EmersonAlbertini/PROJETO-DE-BANCO-DE-CAPACITORES-PARA-CORRECAO-DO-FATOR-DE-POTENCIA-EM-UMA-INDUSTRIA-ALIMENTICIA-/Cálculo_de_Climatização/PROJETO DE BANCO DE CAPACITORES - 225kVAr_20250828_020039_documentation.pdf

# RiTherm

# Summary

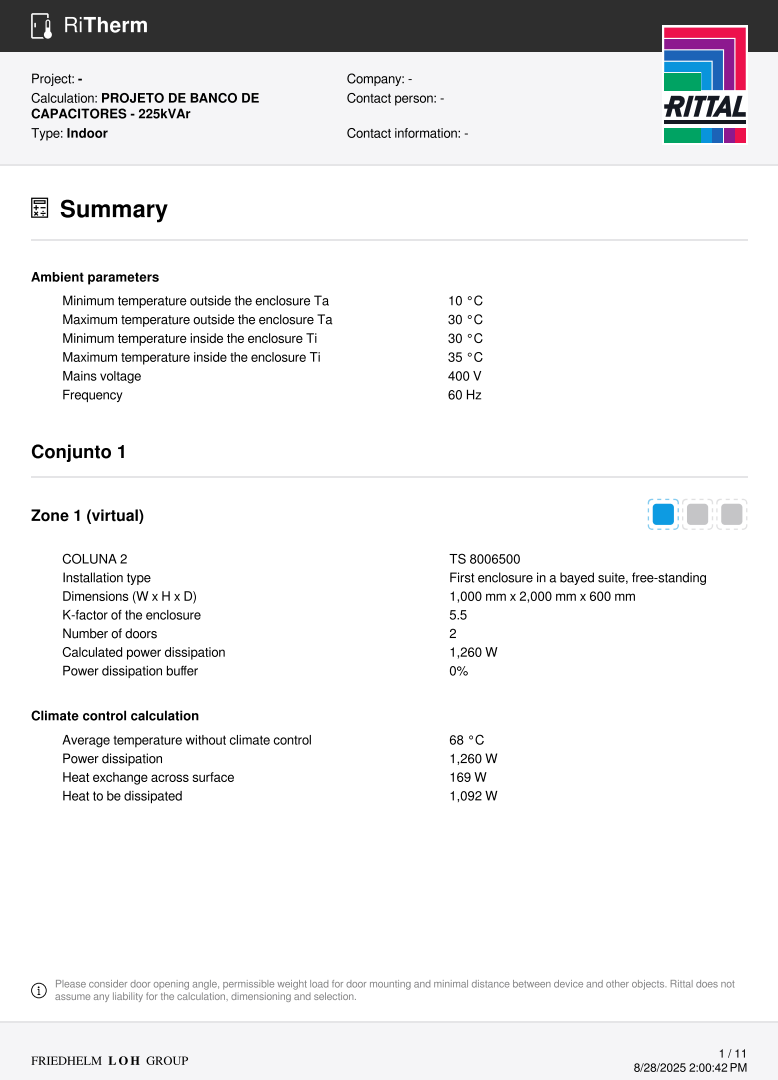
[picture p50: page 1]
Company: -; Contact person: -; Contact information: -; Ambient parameters; Minimum temperature outside the enclosure Ta; Maximum temperature outside the enclosure Ta; Minimum temperature inside the enclosure Ti; Maximum temperature inside the enclosure Ti; Mains voltage; Frequency; Conjunto 1; Zone 1 (virtual); COLUNA 2; Installation type; First enclosure in a bayed suite, free-standing; Dimensions (W x H x D); K-factor of the enclosure; Number of doors; Calculated power dissipation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

Project: -
Calculation: PROJETO DE BANCO DE
CAPACITORES - 225kVAr
Type: Indoor

Climate control calculation

Please consider door opening angle, permissible weight load for door mounting and minimal distance between device and other objects. Rittal does not
assume any liability for the calculation, dimensioning and selection.

## Order overview

Measures to maintain the temperature

The chosen climate control solution for this virtual zone has a different IP rating than the ones in neighbouring zones.

Part number | SK3244740 + SK3243300 chopped-fibre filter
Device type | Fan-and-filter unit
Cooling output | 1,174 m³/h
Necessary air throughput | 765 m³/h
Device mounting | Wall-mounted
IP rating | 54
Quantity | 2

### Zone 2 (virtual)

COLUNA 3 | TS 8606500
Installation type | Enclosure within a bayed suite, free-standing
Dimensions (W x H x D) | 600 mm x 2,000 mm x 600 mm
K-factor of the enclosure | 5.5
Number of doors | 1
Calculated power dissipation | 650 W
Power dissipation buffer | 0%

Climate control calculation

Average temperature without climate control | 61 °C
Power dissipation | 650 W
Heat exchange across surface | 107 W
Heat to be dissipated | 544 W

Please consider door opening angle, permissible weight load for door mounting and minimal distance between device and other objects. Rittal does not assume any liability for the calculation, dimensioning and selection.

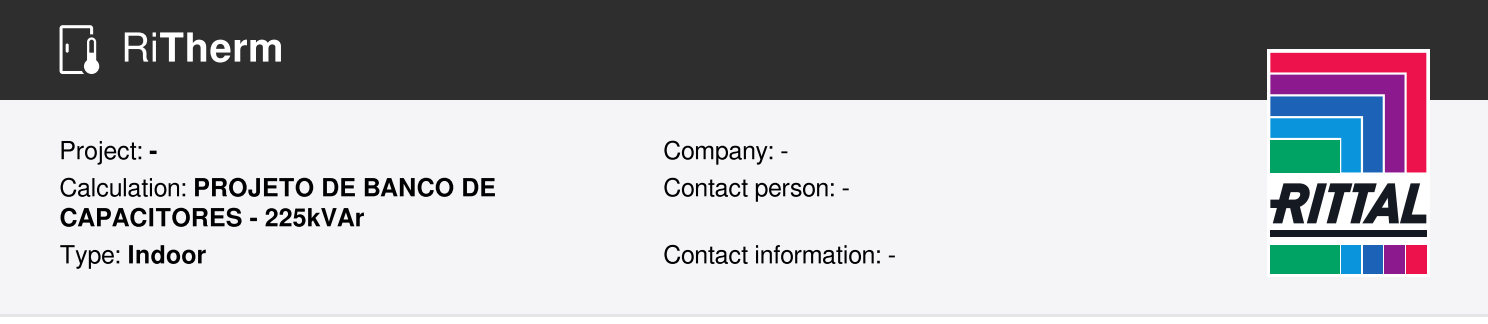
[picture p51: figure]
Calculation: PROJETO DE BANCO DE CAPACITORES - 225kVAr Type: Indoor; Contact person: -; Contact information: -

## Order overview

Measures to maintain the temperature

The chosen climate control solution for this virtual zone has a different IP rating than the ones in neighbouring zones.

Part number | SK3140140 + SK3243200 chopped-fibre filter
Device type | Fan-and-filter unit
Cooling output | 565 m³/h
Air throughput, unimpeded air flow | 853 m³/h
Necessary air throughput | 381 m³/h
Device mounting | Roof-mounted
IP rating | 55
Quantity | 1

### Zone 3 (virtual)

COLUNA 4 | TS 8606500
Installation type | Last enclosure in a bayed suite, free-standing
Dimensions (W x H x D) | 600 mm x 2,000 mm x 600 mm
K-factor of the enclosure | 5.5
Number of doors | 1
Calculated power dissipation | 650 W
Power dissipation buffer | 0%

Climate control calculation

Average temperature without climate control | 58 °C
Power dissipation | 650 W
Heat exchange across surface | 120 W
Heat to be dissipated | 531 W

Please consider door opening angle, permissible weight load for door mounting and minimal distance between device and other objects. Rittal does not assume any liability for the calculation, dimensioning and selection.

## Order overview

Measures to maintain the temperature

The chosen climate control solution for this virtual zone has a different IP rating than the ones in neighbouring zones.

Part number | SK3140140 + SK3243200 chopped-fibre filter
Device type | Fan-and-filter unit
Cooling output | 565 m³/h
Air throughput, unimpeded air flow | 853 m³/h
Necessary air throughput | 372 m³/h
Device mounting | Roof-mounted
IP rating | 55
Quantity | 1

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

# Component list

## Enclosure set: Conjunto 1 (Zone 1)

## COLUNA 2 - TS 8006500

No component list was created for this enclosure. The calculation was performed using the entered power dissipation and simultaneity factor.

Entered power
dissipation

Entered simultaneity
factor
| | Power dissipation buffer | Calculated power dissipation
1,260 W | 100% | 0% | 1,260 W

## Enclosure set: Conjunto 1 (Zone 2)

## COLUNA 3 - TS 8606500

No component list was created for this enclosure. The calculation was performed using the entered power dissipation and simultaneity factor.

Entered power dissipation | Entered simultaneity factor | Power dissipation buffer | Calculated power dissipation
650 W | 100% | 0% | 650 W

## Enclosure set: Conjunto 1 (Zone 3)

## COLUNA 4 - TS 8606500

No component list was created for this enclosure. The calculation was performed using the entered power dissipation and simultaneity factor.

Entered power dissipation | Entered simultaneity factor | Power dissipation buffer | Calculated power dissipation
650 W | 100% | 0% | 650 W

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

Verification of temperature rise according to IEC 60890, as required in DIN EN 61439

Customer / order: PROJETO DE BANCO DE CAPACITORES - 225kVAr - Conjunto 1 - Zone 1 Enclosure type: Single enclosure COLUNA 2 (8006500)

Decisive dimensions for temperature
rise

Height: 2,000 mm
Width: 1,000 mm
Depth: 600 mm

Installation type: Single enclosure, free-standing

Decisive dimensions for temperature rise | | Dimensions | A0 | Area factor b acc. to table 3 | Ae (Sp. 3) x (Sp. 4)
| | m x m | m² | | m²
| | 2 | 3 | 4 | 5
| Roof | 1.00 x 0.60 | 0.60 | 0.90 | 0.54
| Floor | 1.00 x 0.60 | 0.60 | 0.50 | 0.30
| Front | 1.00 x 2.00 | 2.00 | 0.90 | 1.80
| Rear | 1.00 x 2.00 | 2.00 | 0.90 | 1.80
| Left side | 0.60 x 2.00 | 1.20 | 0.90 | 1.08
| Right side | 0.60 x 2.00 | 1.20 | 0.50 | 0.60

Ae = ∑(AO - b) = 6.12

With effective cooling surface Ae
> 1.25 m² | ≤ 1.25 m²
ƒ = h¹.35 ÷ Ab = 4.25 (see 5.2.3) | g = h ÷ w = (see 5.2.3)
Air inlet openings [cm²] | 0
Enclosure constant k | 0.144
Factor for horizontal divider panels d | 1.00
Effective power dissipation W | 1,260.00
P x = P*** | 310.96
Δt0.5 = k × d × Px [K] | 44.68
Temperature distribution factor c | 1.39
Δt1.0 = c × Δt 0.5 [K] | 62.04

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

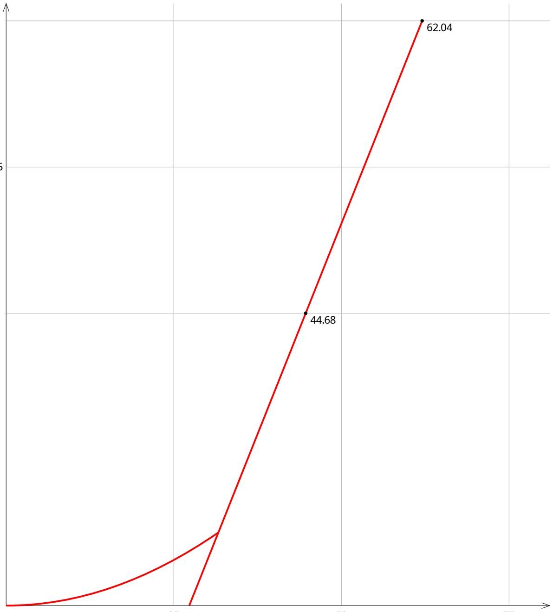
[picture p52: figure]

25 | 50 | 75

1.0

0.75

0.5

### Excess air temperature Δt inside the enclosure →

### Multiple of enclosure height →

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

Verification of temperature rise according to IEC 60890, as required in DIN EN 61439

Customer / order: PROJETO DE BANCO DE CAPACITORES - 225kVAr - Conjunto 1 - Zone 2 Enclosure type: Single enclosure COLUNA 3 (8606500)

Decisive dimensions for temperature
rise

Height: 2,000 mm
Width: 600 mm
Depth: 600 mm

Installation type: Single enclosure, free-standing

Decisive dimensions for temperature rise | | Dimensions | A0 | Area factor b acc. to table 3 | Ae (Sp. 3) x (Sp. 4)
| | m x m | m² | | m²
| | 2 | 3 | 4 | 5
| Roof | 0.60 x 0.60 | 0.36 | 0.90 | 0.32
| Floor | 0.60 x 0.60 | 0.36 | 0.50 | 0.18
| Front | 0.60 x 2.00 | 1.20 | 0.90 | 1.08
| Rear | 0.60 x 2.00 | 1.20 | 0.90 | 1.08
| Left side | 0.60 x 2.00 | 1.20 | 0.50 | 0.60
| Right side | 0.60 x 2.00 | 1.20 | 0.50 | 0.60

Ae = ∑(AO - b) = 3.86

With effective cooling surface Ae
> 1.25 m² | ≤ 1.25 m²
ƒ = h¹.35 ÷ Ab = 7.08 (see 5.2.3) | g = h ÷ w = (see 5.2.3)
Air inlet openings [cm²] | 0
Enclosure constant k | 0.205
Factor for horizontal divider panels d | 1.00
Effective power dissipation W | 650.00
P x = P*** | 182.63
Δt0.5 = k × d × Px [K] | 37.49
Temperature distribution factor c | 1.49
Δt1.0 = c × Δt 0.5 [K] | 55.78

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

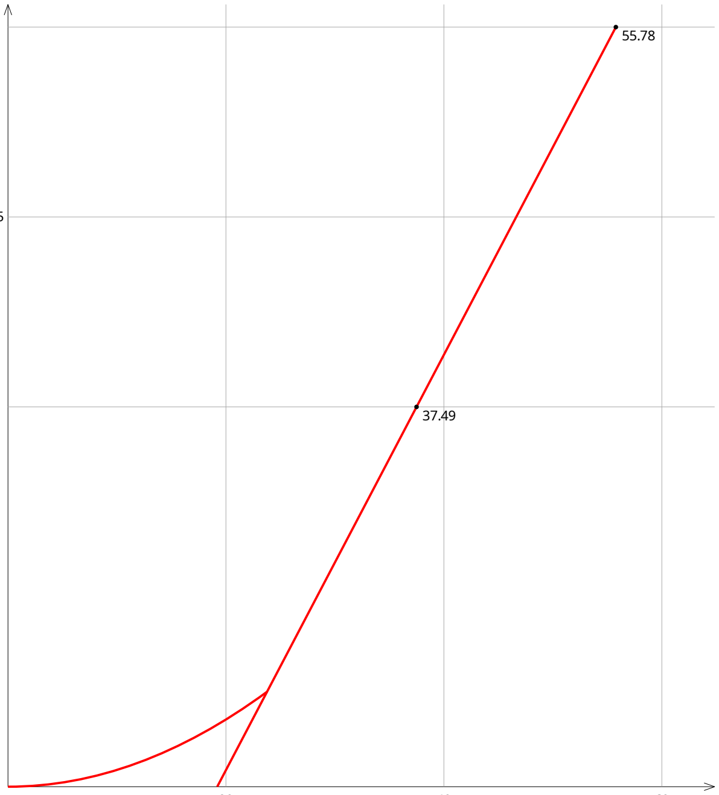
[picture p53: figure]

20 | 40 | 60

1.0

0.75

0.5

### Excess air temperature Δt inside the enclosure →

### Multiple of enclosure height →

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

Verification of temperature rise according to IEC 60890, as required in DIN EN 61439

Customer / order: PROJETO DE BANCO DE CAPACITORES - 225kVAr - Conjunto 1 - Zone 3 Enclosure type: Single enclosure COLUNA 4 (8606500)

Decisive dimensions for temperature
rise

Height: 2,000 mm
Width: 600 mm
Depth: 600 mm

Installation type: Single enclosure, free-standing

Decisive dimensions for temperature rise | | Dimensions | A0 | Area factor b acc. to table 3 | Ae (Sp. 3) x (Sp. 4)
| | m x m | m² | | m²
| | 2 | 3 | 4 | 5
| Roof | 0.60 x 0.60 | 0.36 | 0.90 | 0.32
| Floor | 0.60 x 0.60 | 0.36 | 0.50 | 0.18
| Front | 0.60 x 2.00 | 1.20 | 0.90 | 1.08
| Rear | 0.60 x 2.00 | 1.20 | 0.90 | 1.08
| Left side | 0.60 x 2.00 | 1.20 | 0.50 | 0.60
| Right side | 0.60 x 2.00 | 1.20 | 0.90 | 1.08

Ae = ∑(AO - b) = 4.34

With effective cooling surface Ae
> 1.25 m² | ≤ 1.25 m²
ƒ = h¹.35 ÷ Ab = 7.08 (see 5.2.3) | g = h ÷ w = (see 5.2.3)
Air inlet openings [cm²] | 0
Enclosure constant k | 0.187
Factor for horizontal divider panels d | 1.00
Effective power dissipation W | 650.00
P x = P*** | 182.63
Δt0.5 = k × d × Px [K] | 34.24
Temperature distribution factor c | 1.49
Δt1.0 = c × Δt 0.5 [K] | 50.94

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

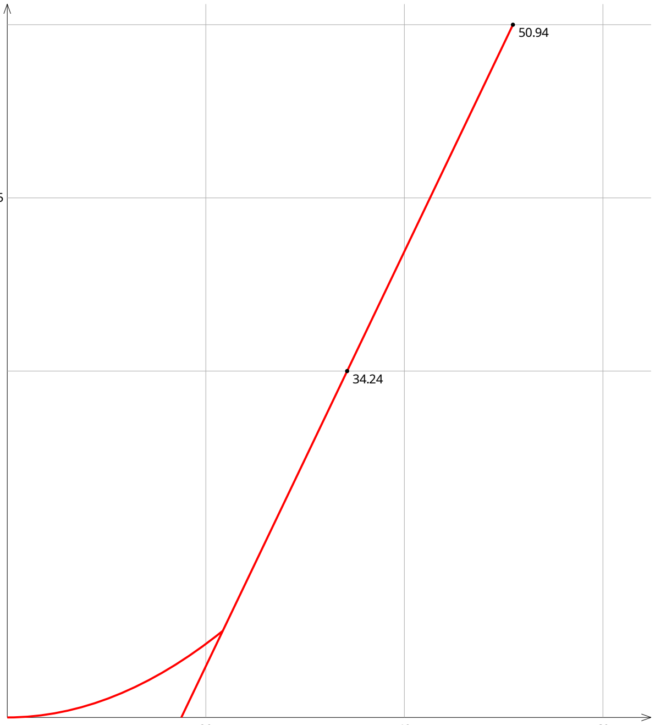
[picture p54: figure]

20 | 40 | 60

1.0

0.75

0.5

### Excess air temperature Δt inside the enclosure →

### Multiple of enclosure height →

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
